dishishshawn/ESP32Pet/src/sprites.h

#ifndef Sprites_h
#define Sprites_h

#include <Arduino.h>

// 'beard', 10x10px
const unsigned char beard_icon [] PROGMEM = {
  0x00, 0x00, 0x80, 0x40, 0x9e, 0x40, 0x92, 0x40, 0xc0, 0xc0, 0xcc, 0xc0, 0xff, 0xc0, 0x7f, 0x80, 
  0x3f, 0x00, 0x00, 0x00
};

// 'dress', 10x10px
const unsigned char dress_icon [] PROGMEM = {
  0x00, 0x00, 0xe1, 0xc0, 0x9e, 0x40, 0x80, 0x40, 0xc0, 0xc0, 0x21, 0x00, 0x21, 0x00, 0x21, 0x00, 
  0x3f, 0x00, 0x00, 0x00
};
// 'eat', 10x10px
const unsigned char eat_icon [] PROGMEM = {
  0x01, 0x80, 0x0d, 0xc0, 0x13, 0xc0, 0x21, 0x00, 0x40, 0x80, 0x40, 0x80, 0x21, 0x00, 0xf2, 0x00, 
	0xec, 0x00, 0x60, 0x00
};
// 'hair', 10x10px
const unsigned char stats_icon [] PROGMEM = {
  0x7f, 0x80, 0x40, 0x80, 0x5e, 0x80, 0x40, 0x80, 0x5e, 0x80, 0x40, 0x80, 0x5e, 0x80, 0x40, 0x80, 
	0x41, 0x00, 0x7e, 0x00
};
// 'play', 10x10px
const unsigned char play_icon [] PROGMEM = {
  0x1e, 0x00, 0x21, 0x00, 0x40, 0x80, 0x92, 0x40, 0x80, 0x40, 0x92, 0x40, 0x8c, 0x40, 0x40, 0x80, 
	0x21, 0x00, 0x1e, 0x00
};
// 'sleep', 10x10px
const unsigned char sleep_icon [] PROGMEM = {
  0x00, 0x00, 0x78, 0x00, 0x08, 0x00, 0x10, 0x00, 0x27, 0x80, 0x40, 0x80, 0x79, 0x00, 0x02, 0x00, 
  0x04, 0x00, 0x07, 0x80
};

//_____________________________ BEARD

const unsigned char beard [] PROGMEM = {
  0x00, 0x00, 0x00, 0x00, 0x00, 0x00, 0x00, 0x00, 0x00, 0x00, 0x00, 0x00, 0x00, 0x00, 0x00, 0x00, 
  0x00, 0x00, 0x00, 0x00, 0x00, 0x00, 0x00, 0x00, 0x00, 0x00, 0x00, 0x00, 0x00, 0x00, 0x00, 0x00, 
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
	0x12, 0x00, 0x00, 0x00, 0x87, 0xe2, 0x00, 0x00, 0x00, 0x40, 0x04, 0x00, 0x00, 0x00, 0x20, 0x18, 
	0x00, 0x00, 0x00, 0x1f, 0xe0, 0x00, 0x00, 0x00, 0x00, 0x00, 0x00, 0x00, 0x00, 0x00, 0x00, 0x00, 
	0x00, 0x00, 0x00, 0x00, 0x00, 0x00, 0x00, 0x00, 0x00, 0x00, 0x00, 0x00
};

#endif
